rmaryan/MSFS2020-Ardunio-Cockpit/extra/schematics/schematics.kicad_sch

## KiCad design extra/schematics/schematics.kicad_sch (2022-09-19)

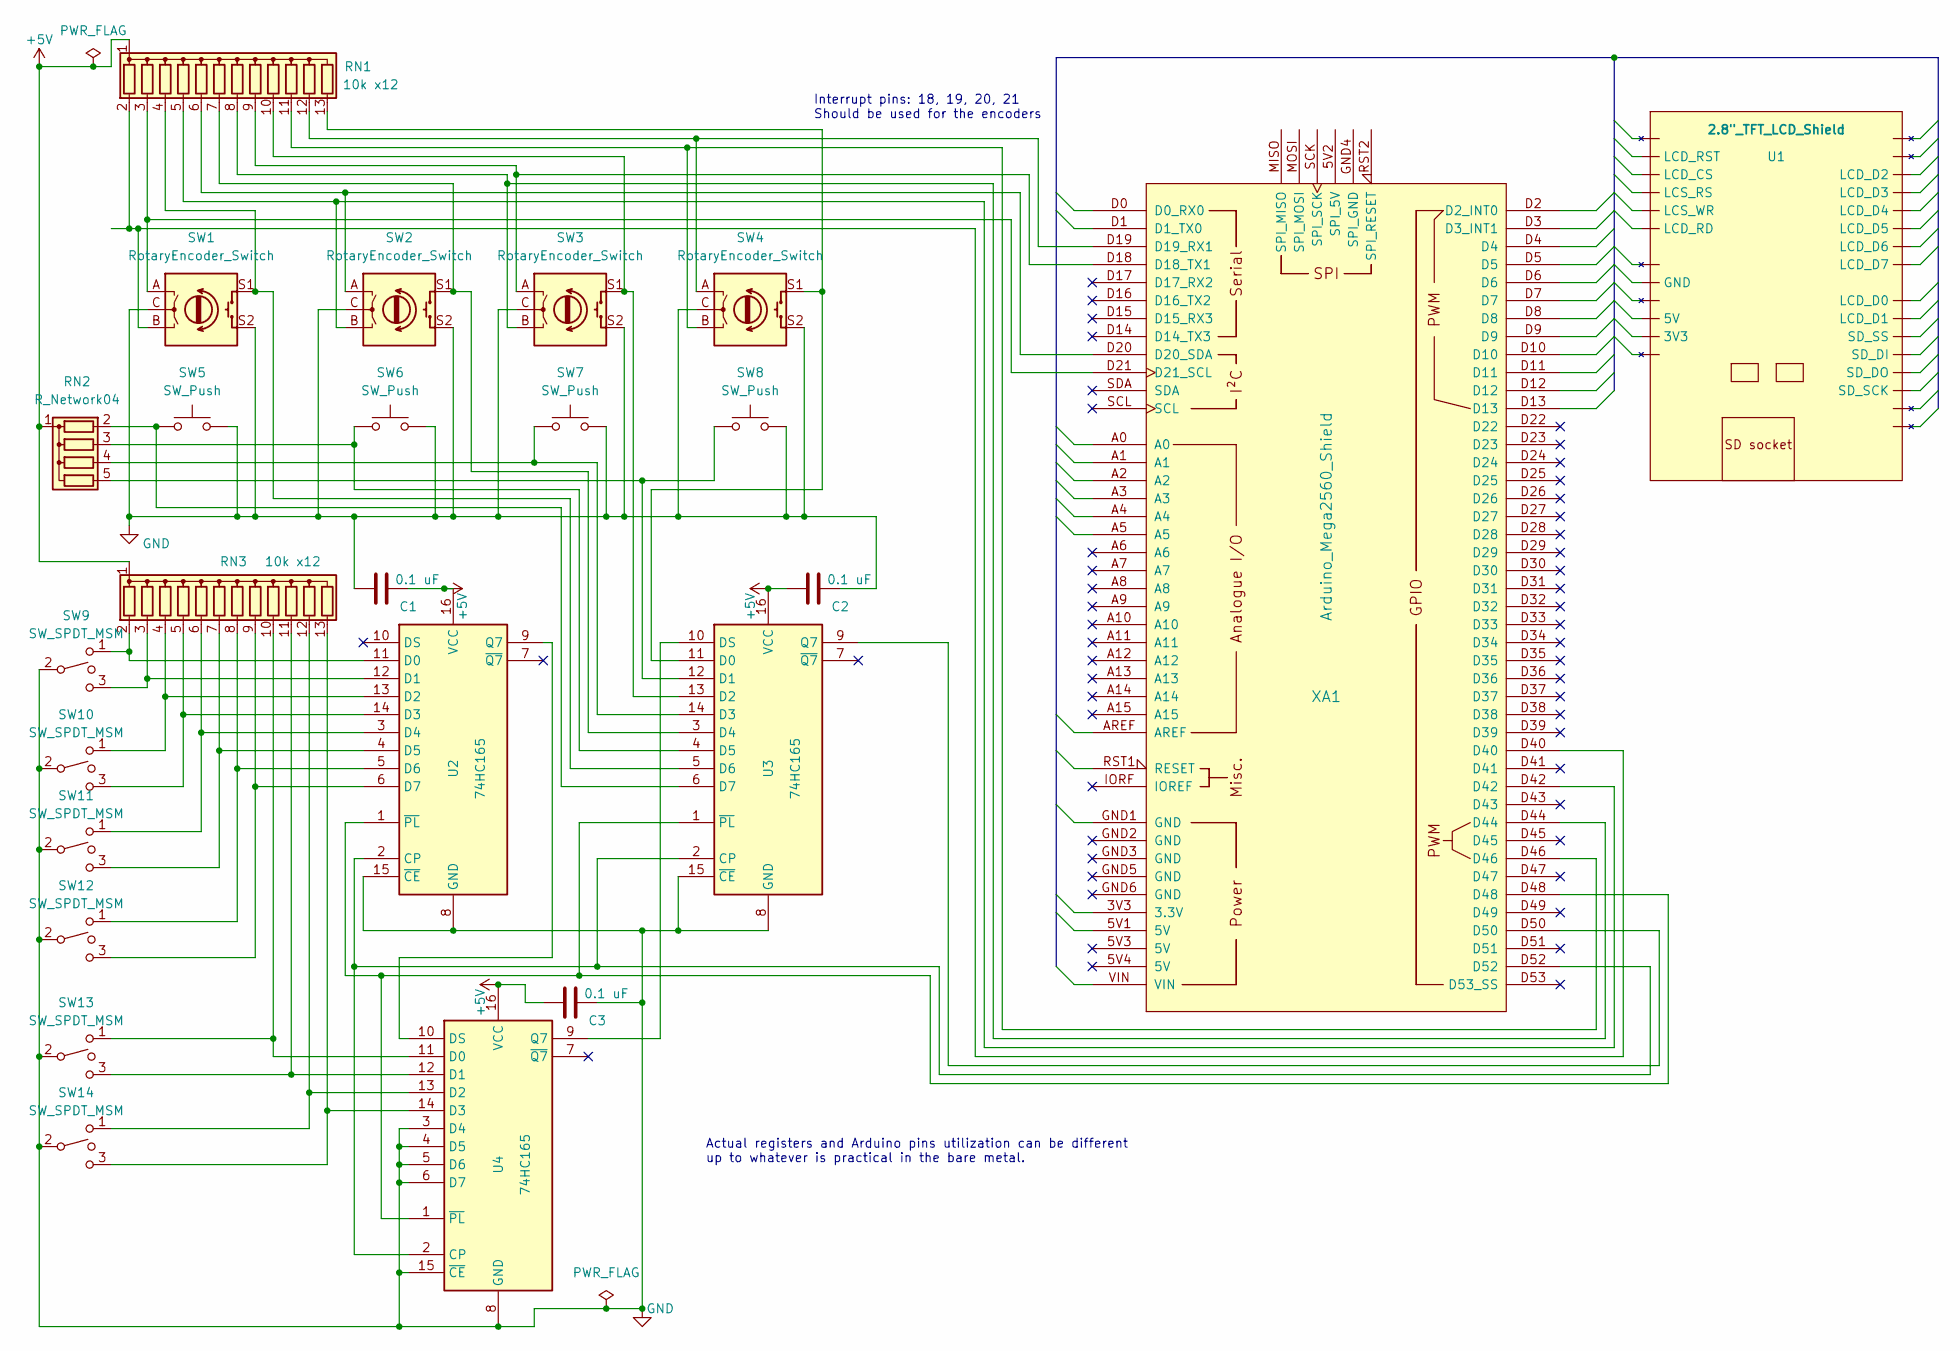
[picture p10: schematic schematics.kicad_sch]

Parts:
C1, C2, C3: 0.1 uF
RN1, RN3: 10k x12; R_Array_SIP13
RN2: R_Network04; R_Array_SIP5
SW1, SW2, SW3, SW4: RotaryEncoder_Switch
SW5, SW6, SW7, SW8: SW_Push
SW9, SW10, SW11, SW12, SW13, SW14: SW_SPDT_MSM
U1: 2.8"_TFT_LCD_Shield
U2, U3, U4: 74HC165
XA1: Arduino_Mega2560_Shield

Connections:
+5V: C1.2, C2.1, C3.1, RN1.1 (common), RN2.1 (common), RN3.1 (common), U2.16 (VCC), U3.16 (VCC), U4.16 (VCC)
GND: C1.1, C2.2, C3.2, SW1.C, SW1.S2, SW2.C, SW2.S2, SW3.C, SW3.S2, SW4.C, SW4.S2, SW5.2, SW6.2, SW7.2, SW8.2, SW9.2, SW10.2, SW11.2, SW12.2, SW13.2, SW14.2, U2.8 (GND), U2.15 (~CE), U3.8 (GND), U3.15 (~CE), U4.3 (D4), U4.4 (D5), U4.5 (D6), U4.6 (D7), U4.8 (GND), U4.15 (~CE)
unnamed: RN1.2 (R1), SW1.B, XA1.D40
unnamed: RN1.3 (R2), SW1.A, XA1.D21 (D21_SCL)
unnamed: RN1.4 (R3), SW1.S1, U3.5 (D6)
unnamed: RN1.5 (R4), SW2.B, XA1.D42
unnamed: RN1.6 (R5), SW2.A, XA1.D20 (D20_SDA)
unnamed: RN1.7 (R6), SW2.S1, U3.3 (D4)
unnamed: RN1.8 (R7), SW3.B, XA1.D44
unnamed: RN1.9 (R8), SW3.A, XA1.D18 (D18_TX1)
unnamed: RN1.10 (R9), SW3.S1, U3.13 (D2)
unnamed: RN1.11 (R10), SW4.B, XA1.D46
unnamed: RN1.12 (R11), SW4.A, XA1.D19 (D19_RX1)
unnamed: RN1.13 (R12), SW4.S1, U3.11 (D0)
unnamed: RN2.2 (R1), SW5.1, U3.6 (D7)
unnamed: RN2.3 (R2), SW6.1, U3.4 (D5)
unnamed: RN2.4 (R3), SW7.1, U3.14 (D3)
unnamed: RN2.5 (R4), SW8.1, U3.12 (D1)
unnamed: RN3.2 (R1), SW9.1, U2.11 (D0)
unnamed: RN3.3 (R2), SW9.3, U2.12 (D1)
unnamed: RN3.4 (R3), SW10.1, U2.13 (D2)
unnamed: RN3.5 (R4), SW10.3, U2.14 (D3)
unnamed: RN3.6 (R5), SW11.1, U2.3 (D4)
unnamed: RN3.7 (R6), SW11.3, U2.4 (D5)
unnamed: RN3.8 (R7), SW12.1, U2.5 (D6)
unnamed: RN3.9 (R8), SW12.3, U2.6 (D7)
unnamed: RN3.10 (R9), SW13.1, U4.11 (D0)
unnamed: RN3.11 (R10), SW13.3, U4.12 (D1)
unnamed: RN3.12 (R11), SW14.1, U4.13 (D2)
unnamed: RN3.13 (R12), SW14.3, U4.14 (D3)
unnamed: U2.1 (~PL), U3.1 (~PL), U4.1 (~PL), XA1.D48
unnamed: U2.2 (CP), U3.2 (CP), U4.2 (CP), XA1.D52
unnamed: U2.9 (Q7), U4.10 (DS)
unnamed: U3.9 (Q7), XA1.D50
unnamed: U3.10 (DS), U4.9 (Q7)

Notes on the sheet:
Actual registers and Arduino pins utilization can be different up to whatever is practical in the bare metal.
Interrupt pins: 18, 19, 20, 21 Should be used for the encoders
